BBZ-AIFS51/LF7-Projekt_GAS/wiki/_Sidebar.md

<!-- Diese Seite wird automatisch aus dem Ordner wiki/ im Repository erzeugt. Änderungen im Wiki-Editor werden beim nächsten Abgleich überschrieben. Bearbeiten: https://github.com/BBZ-AIFS51/LF7-Projekt_GAS/tree/main/wiki -->
### 🔒 Projekt GAS

**Dokumentation**
1. [Deckblatt](Home)
2. [Idee und Zielsetzung](Idee-und-Zielsetzung)
3. [Funktionsbeschreibung](Funktionsbeschreibung)
4. [Verwendete Bauteile](Verwendete-Bauteile)
5. [Aufbau und Schaltplan](Aufbau-und-Schaltplan)
6. [Sourcecode](Sourcecode)
7. [Wichtige Codeabschnitte](Wichtige-Codeabschnitte)
8. [Herausforderungen](Herausforderungen)
9. [Fazit und Ausblick](Fazit-und-Ausblick)
10. [Quellenverzeichnis](Quellenverzeichnis)

**Anhang**
- [👥 Team und Rollen](Team-und-Rollen)
- [📅 Zeitplan](Zeitplan)
- [💶 Kosten](Kosten)
- [🔧 Projektphasen](Projektphasen)
- [🧭 Entwicklungsverlauf](Entwicklungsverlauf)
- [🤖 KI-Einsatz](KI-Einsatz)

---

**Links**
- [▶ 3D-Modell](https://bbz-aifs51.github.io/LF7-Projekt_GAS/)
- [📦 Repository](https://github.com/BBZ-AIFS51/LF7-Projekt_GAS)
- [📄 Anleitung (PDF)](https://github.com/BBZ-AIFS51/LF7-Projekt_GAS/blob/main/Anleitung/Mini%20Security%20System%20Manual.pdf)
