BBZ-AIFS51/LF7-Projekt_GAS/wiki/Fazit-und-Ausblick.md

<!-- Diese Seite wird automatisch aus dem Ordner wiki/ im Repository erzeugt. Änderungen im Wiki-Editor werden beim nächsten Abgleich überschrieben. Bearbeiten: https://github.com/BBZ-AIFS51/LF7-Projekt_GAS/tree/main/wiki -->
# 9 · 💭 Fazit und Ausblick

Was erreicht wurde, was wir gelernt haben und welche Erweiterungen denkbar sind.

## Soll/Ist-Vergleich

Die Anforderungen stehen ausführlich in [Kapitel 2](Idee-und-Zielsetzung#anforderungen).

| Bereich | Ziel | Ergebnis |
|---|---|:---:|
| **Muss** | PIN-Bedienung, Symbole auf dem Display, Töne, Alarm bei Bewegung und nach 3 Fehlversuchen | ✅ 7 / 7 |
| **Kann** | RFID-Karten, Ausgangsverzögerung, Admin-Menü, RFID-Reset, 3D-Modell | ✅ 5 / 6 |
| **Kann** | 3D-gedrucktes Gehäuse | 🟡 entworfen, ✏️ TODO: gedruckt? |
| **Zeit** | Abgabe bis ✏️ TODO | ✏️ TODO |
| **Kosten** | ✏️ TODO (gab es ein Budget?) | siehe [Kosten](Kosten) |

> [!NOTE]
> ✏️ **TODO (Team):** Fazit in 2–3 Sätzen: Hat das Projekt sein Ziel erreicht?
> Was ist das wichtigste Ergebnis?

## Reflexion

> [!IMPORTANT]
> ✏️ **TODO (Team): Reflexion schreiben.** Diesen Abschnitt bitte selbst
> formulieren, ohne KI, er ist eure persönliche Bewertung. Die Fragen unten
> dienen nur als Leitfaden und können danach gelöscht werden.

### Was lief gut?

✏️ TODO

<details>
<summary>Leitfragen</summary>

- Welche Teile des Projekts haben euch am meisten Spaß gemacht?
- Worauf seid ihr stolz?
- Was hat im Team gut funktioniert?

</details>

### Was war schwierig?

✏️ TODO

<details>
<summary>Leitfragen</summary>

- Welche Probleme haben am meisten Zeit gekostet? (z. B. die Neustarts wegen
  des knappen Arbeitsspeichers, siehe [Herausforderungen](Herausforderungen))
- Wo seid ihr nicht weitergekommen und wie habt ihr das gelöst?
- Was hat im Team weniger gut funktioniert?

</details>

### Was haben wir gelernt?

✏️ TODO

<details>
<summary>Leitfragen</summary>

- Fachlich: Mikrocontroller, Bussysteme (I²C, SPI), Speicher, Zustandsautomaten,
  RFID, 3D-Druck
- Methodisch: Fehlersuche Schritt für Schritt, Versionsverwaltung mit Git,
  Dokumentation
- Arbeiten mit KI: Was muss man selbst können, um die KI sinnvoll einzusetzen?
  (siehe [KI-Einsatz](KI-Einsatz))

</details>

### Was würden wir beim nächsten Mal anders machen?

✏️ TODO

<details>
<summary>Leitfragen</summary>

- Planung: Hätte ein Zeitplan von Anfang an geholfen? (siehe [Zeitplan](Zeitplan))
- Technik: Würdet ihr einen anderen Mikrocontroller wählen, z. B. mit mehr
  Speicher und Pins?
- Zusammenarbeit: Aufgaben anders verteilen?

</details>

## Ausblick

> [!NOTE]
> ✏️ **TODO (Team):** 2–4 Ideen auswählen oder eigene ergänzen und kurz
> begründen. Mögliche Erweiterungen:
> - Rollen pro Karte (z. B. darf nur entschärfen oder darf auch Karten anlernen)
> - Protokoll, wer wann welche Karte benutzt hat
> - Sabotagekontakt am Gehäuse
> - Benachrichtigung aufs Handy, z. B. mit einem WLAN-fähigen Mikrocontroller
> - Akku als Notstrom, damit Stecker-Ziehen die Anlage nicht abschaltet

---

<sub>← [8 Herausforderungen](Herausforderungen) · [10 Quellenverzeichnis](Quellenverzeichnis) →</sub>
